durgeshriyaconstruction-sketch/astro-smart-attendance/renders/exploded_iso.png

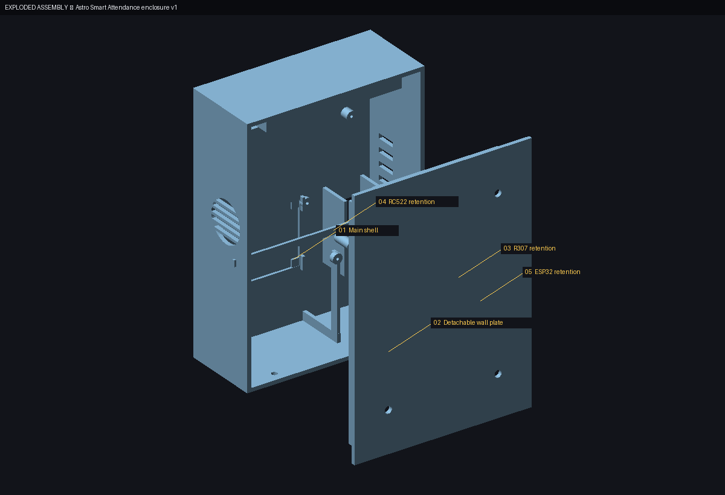
renders/exploded_iso.png
