durgeshriyaconstruction-sketch/astro-smart-attendance/renders/rfid_before_after.png

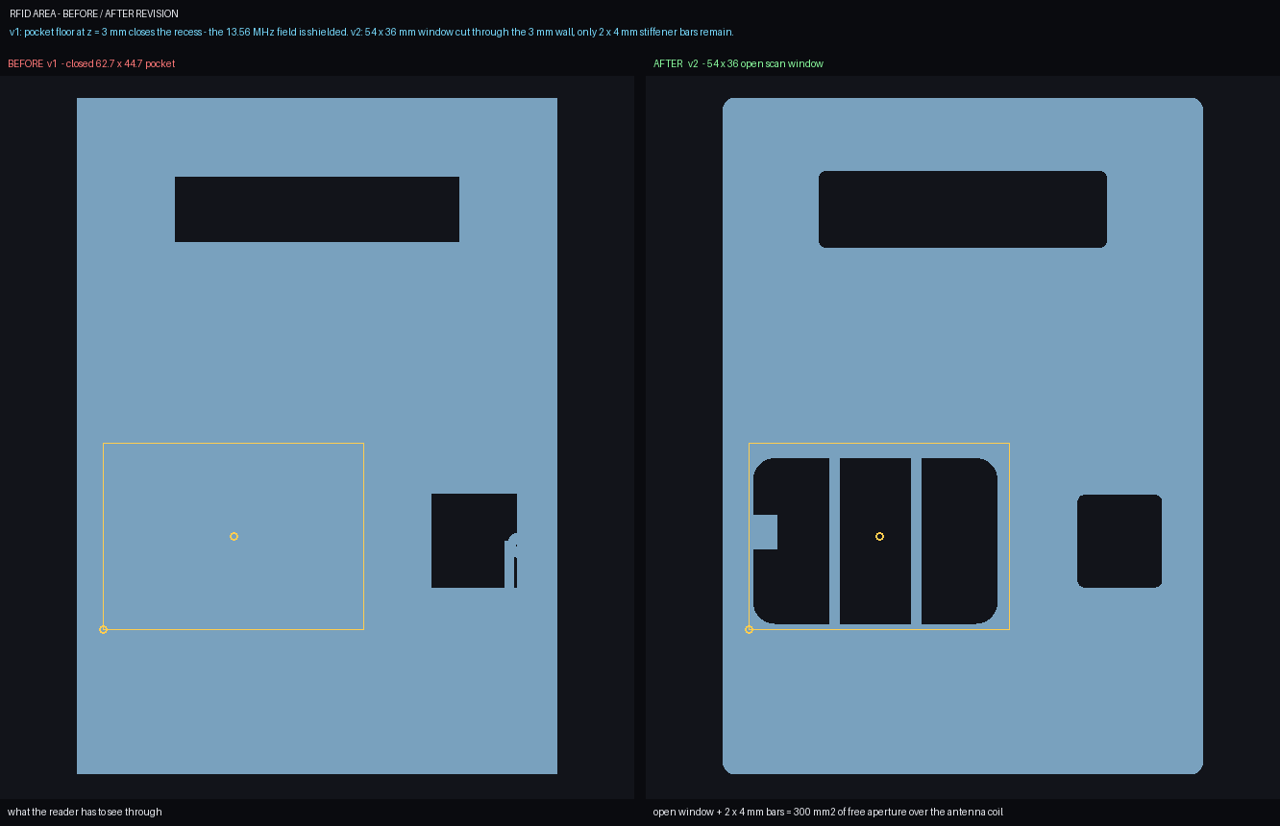
renders/rfid_before_after.png
