durgeshriyaconstruction-sketch/astro-smart-attendance/renders/section_iso.png

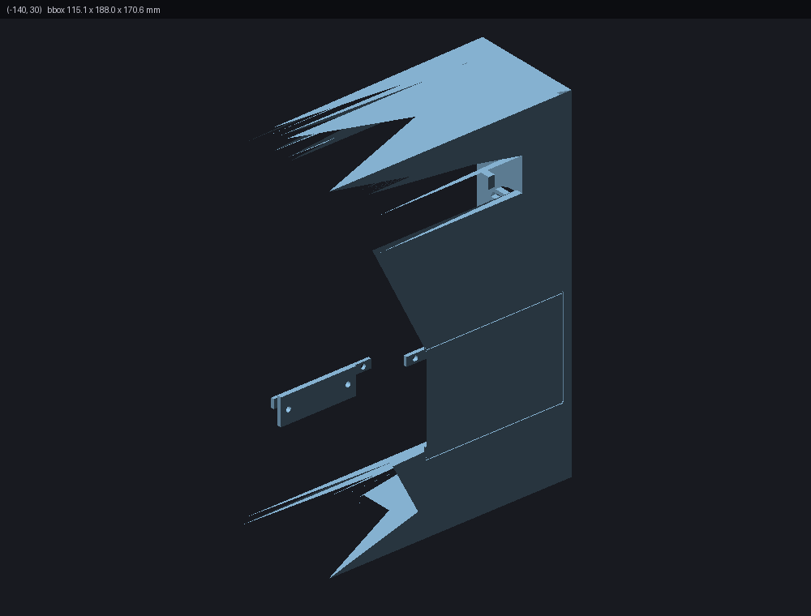
renders/section_iso.png
