durgeshriyaconstruction-sketch/astro-smart-attendance/renders/shell_drawing_sheet.png

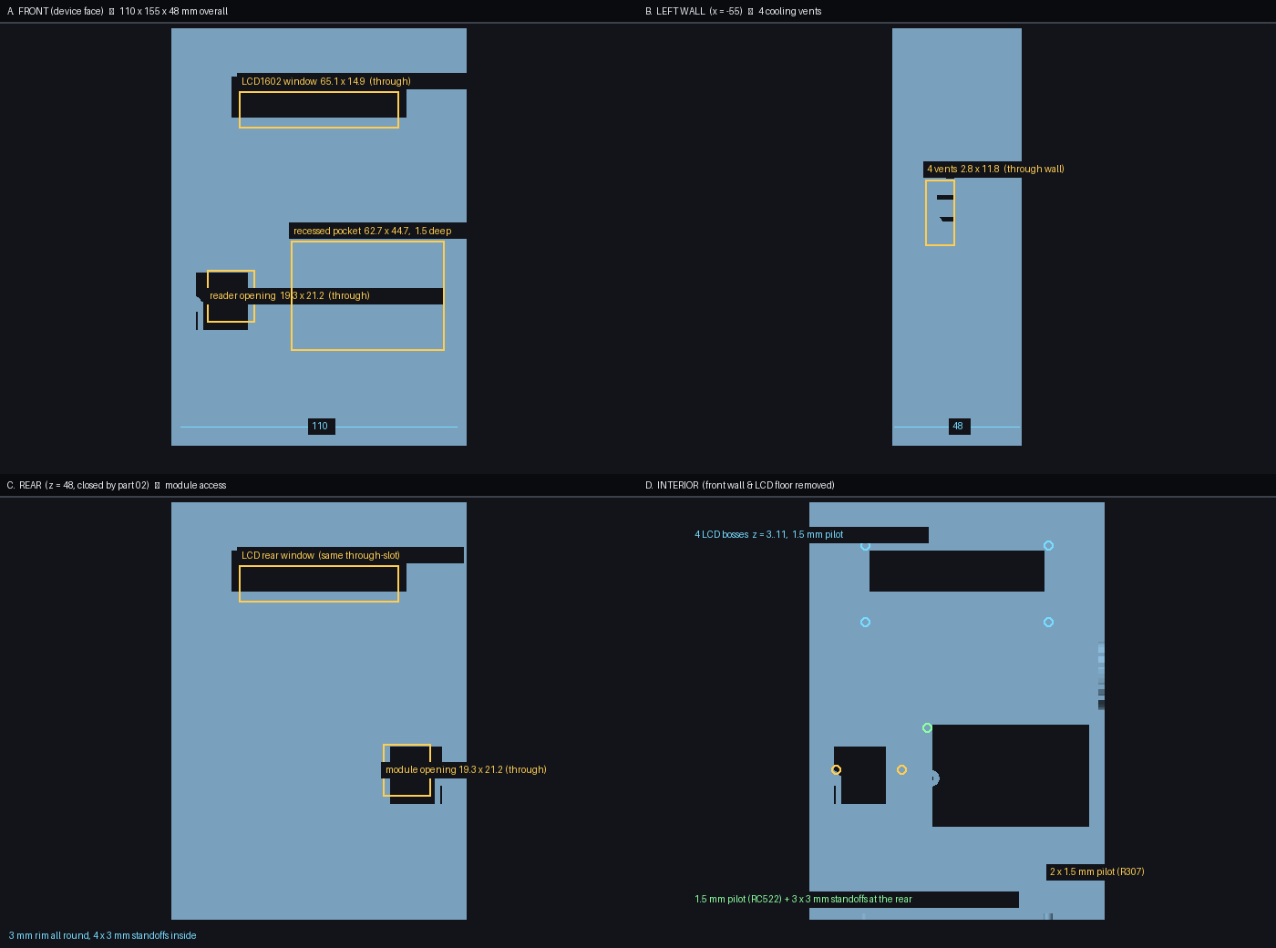
renders/shell_drawing_sheet.png
