durgeshriyaconstruction-sketch/astro-smart-attendance/renders/shell_front.png

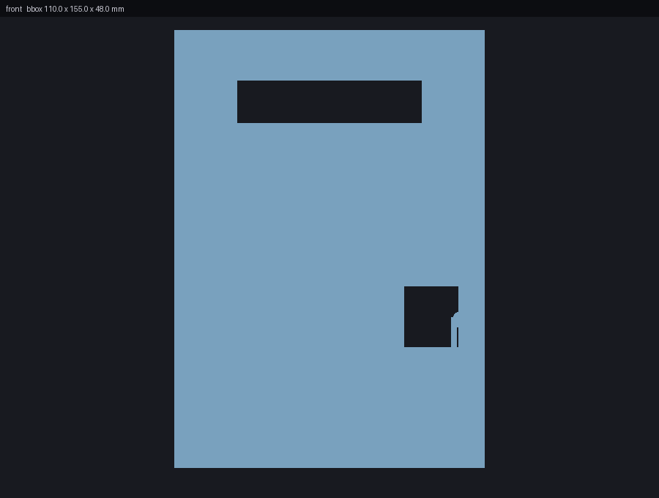
renders/shell_front.png
