durgeshriyaconstruction-sketch/astro-smart-attendance/renders/shell_iso.png

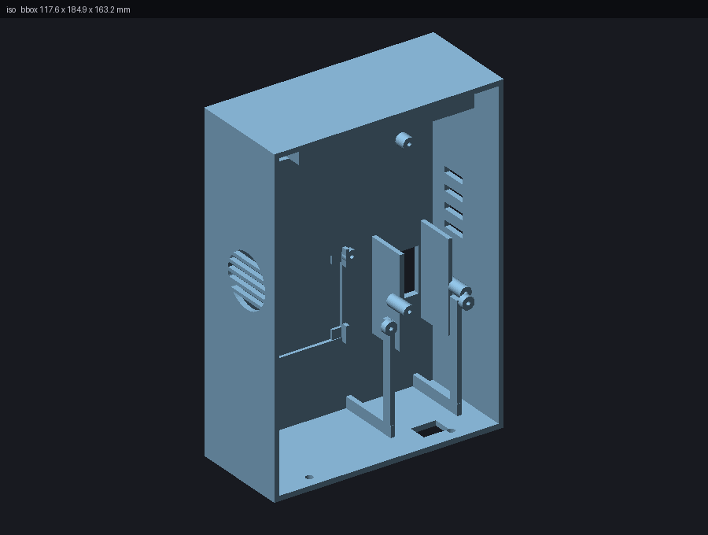
renders/shell_iso.png
