durgeshriyaconstruction-sketch/astro-smart-attendance/renders/shell_side.png

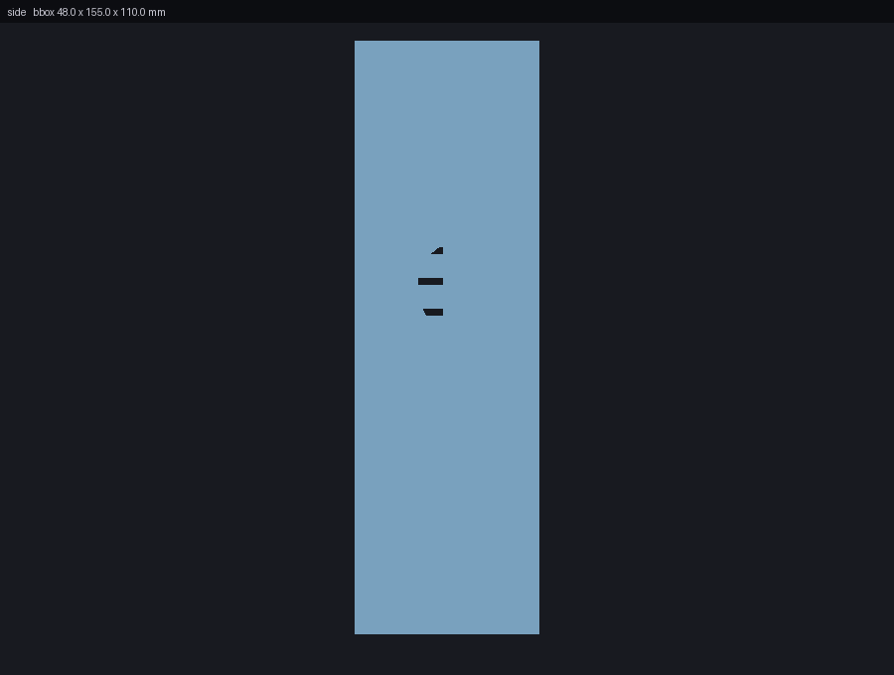
renders/shell_side.png
