durgeshriyaconstruction-sketch/astro-smart-attendance/renders/shell_top.png

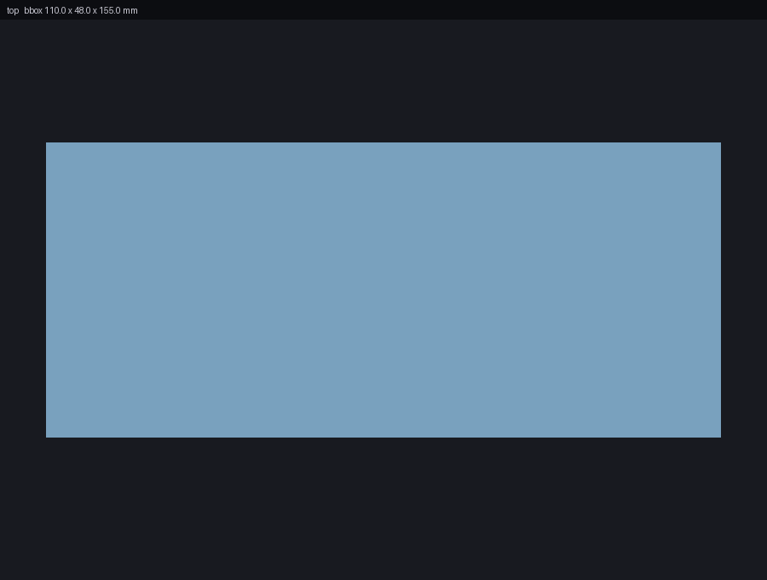
renders/shell_top.png
