durgeshriyaconstruction-sketch/astro-smart-attendance/renders/v2_all_views.png

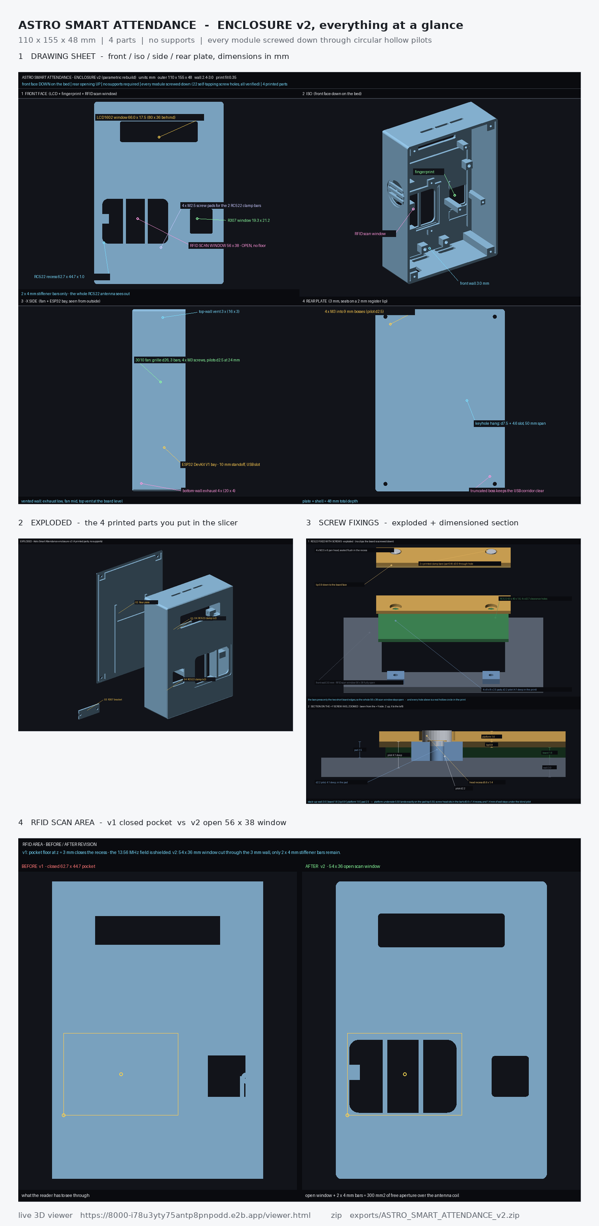
renders/v2_all_views.png
