durgeshriyaconstruction-sketch/astro-smart-attendance/renders/v2_exploded_iso.png

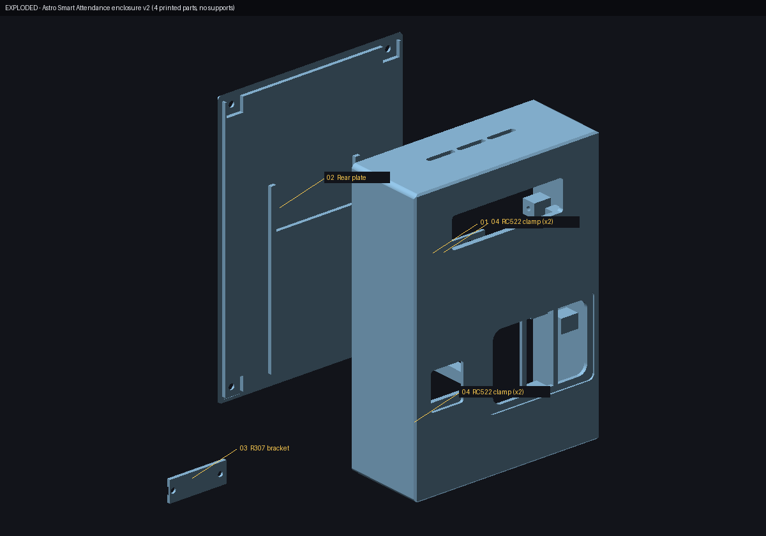
renders/v2_exploded_iso.png
