durgeshriyaconstruction-sketch/astro-smart-attendance/renders/v2_fixing_exploded.png

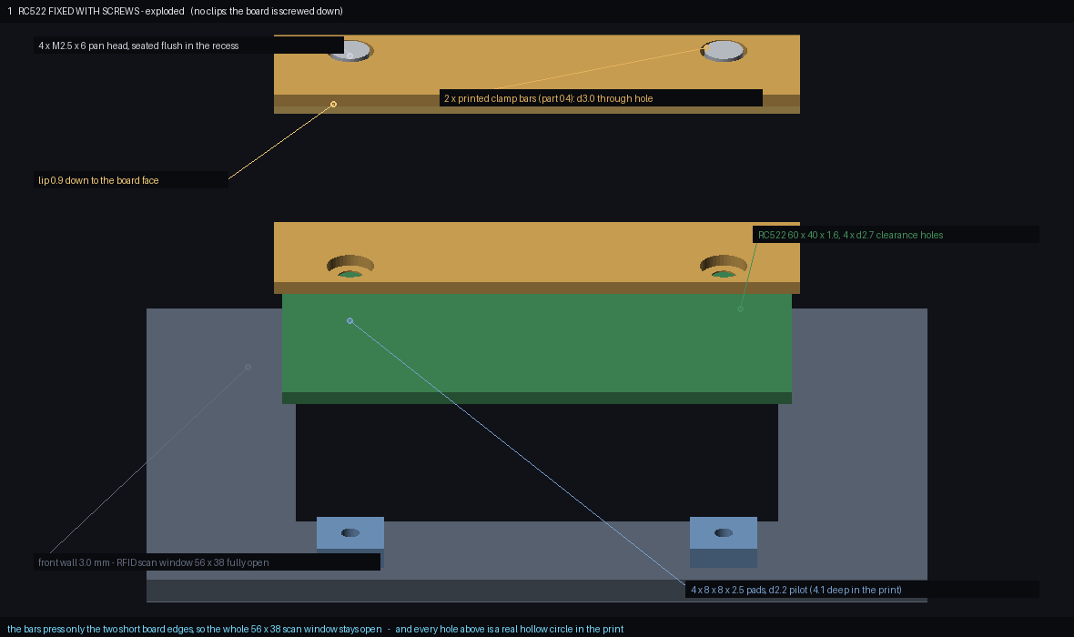
renders/v2_fixing_exploded.png
