durgeshriyaconstruction-sketch/astro-smart-attendance/renders/v2_fixing_section.png

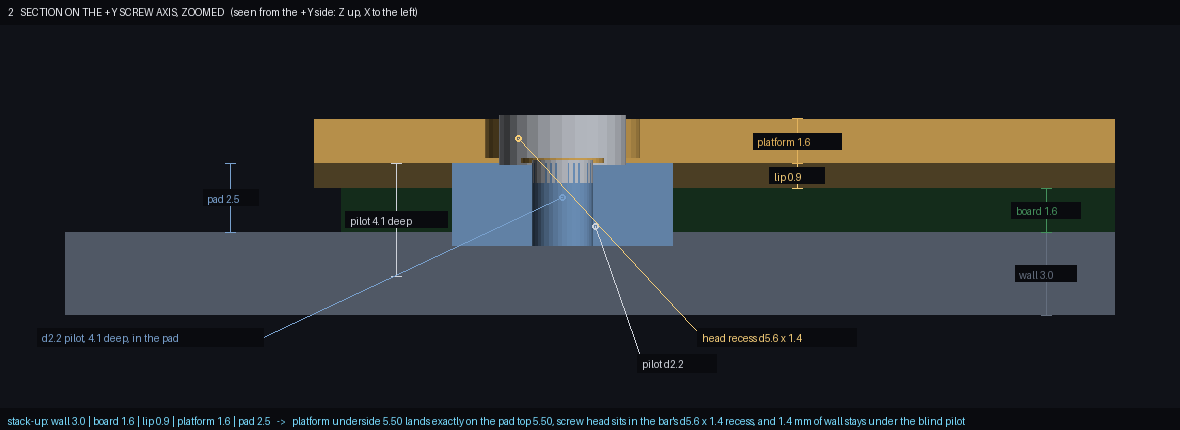
renders/v2_fixing_section.png
