durgeshriyaconstruction-sketch/astro-smart-attendance/renders/v2_shell_drawing_sheet.png

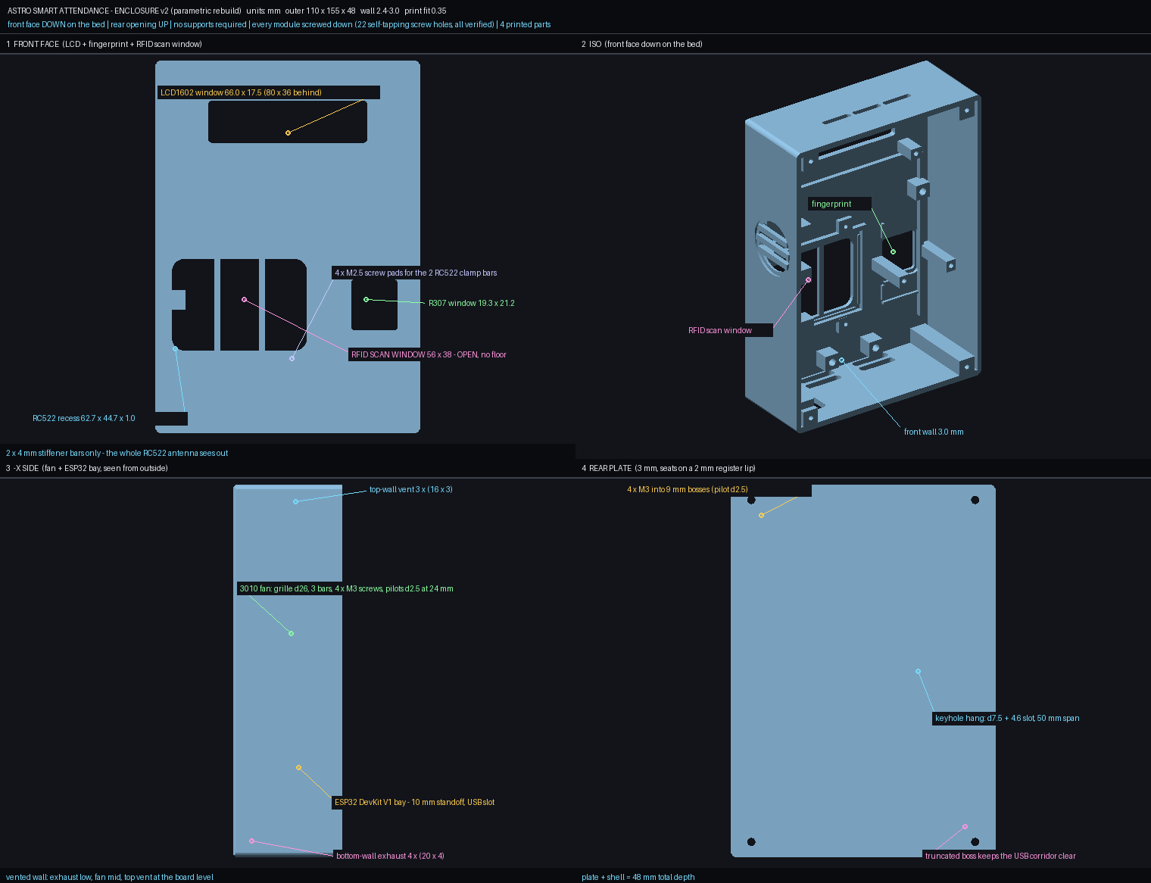
renders/v2_shell_drawing_sheet.png
