durgeshriyaconstruction-sketch/astro-smart-attendance/renders/v3_all_views.png

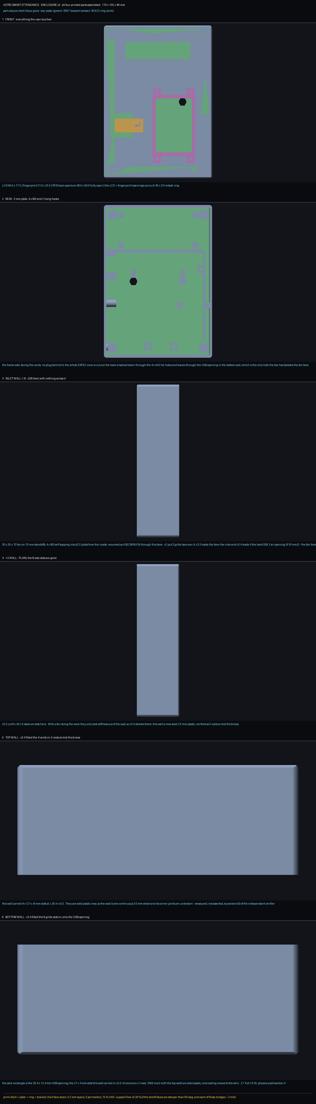
renders/v3_all_views.png
