durgeshriyaconstruction-sketch/astro-smart-attendance/renders/v3_blend_exploded.png

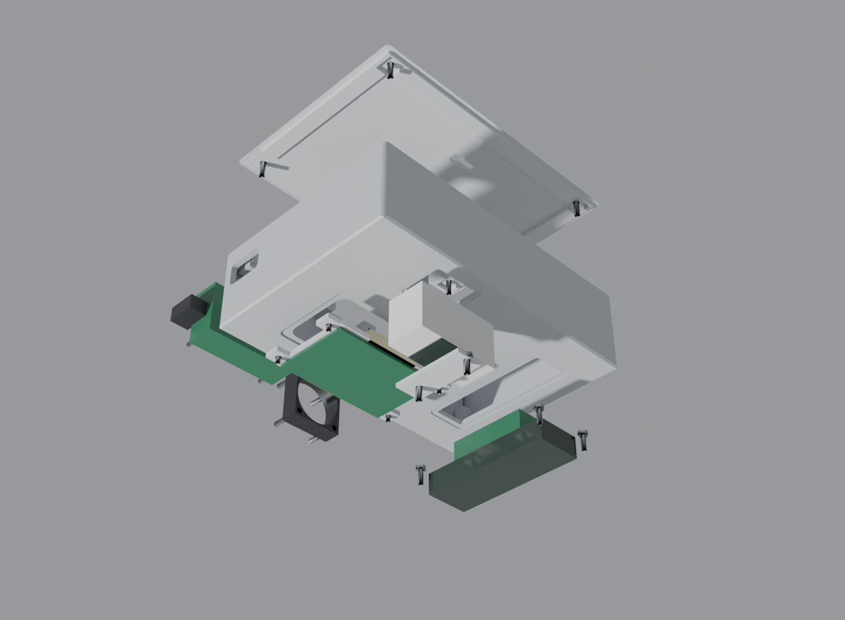
renders/v3_blend_exploded.png
