durgeshriyaconstruction-sketch/astro-smart-attendance/renders/v3_blend_front.png

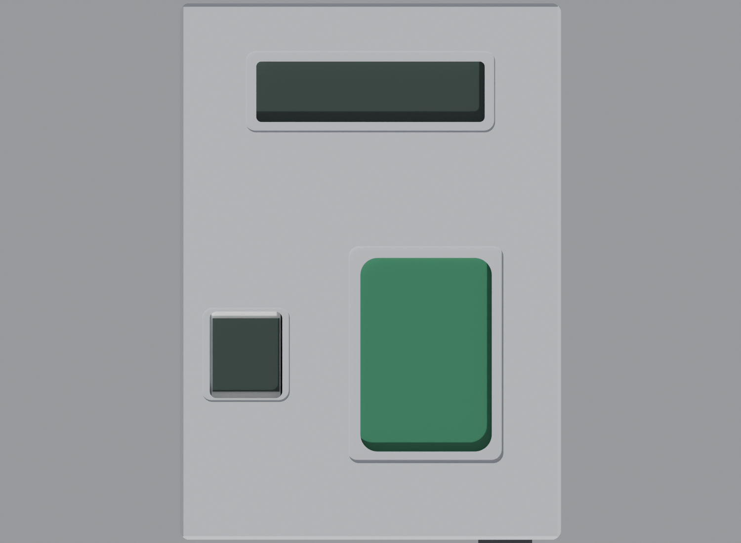
renders/v3_blend_front.png
