durgeshriyaconstruction-sketch/astro-smart-attendance/renders/v3_blend_iso.png

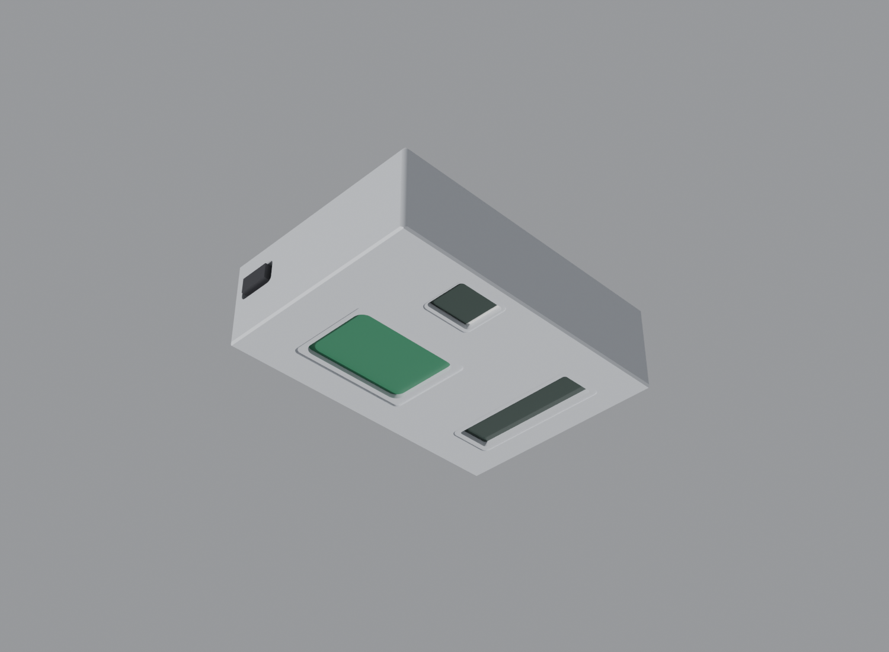
renders/v3_blend_iso.png
