durgeshriyaconstruction-sketch/astro-smart-attendance/renders/v3_fixing_detail.png

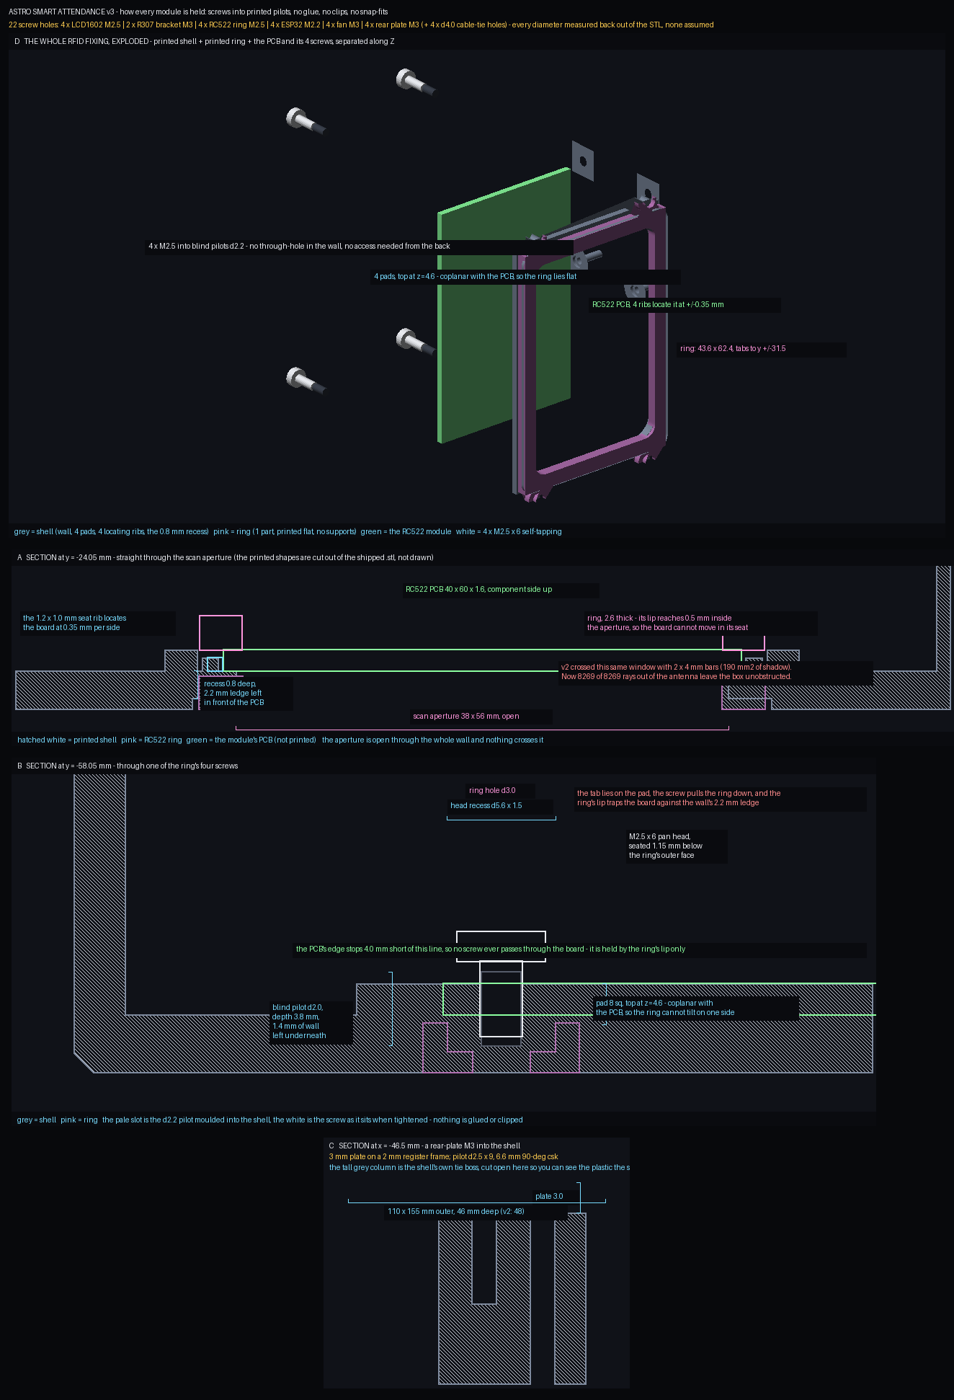
renders/v3_fixing_detail.png
