durgeshriyaconstruction-sketch/astro-smart-attendance/renders/v3_grille_map.png

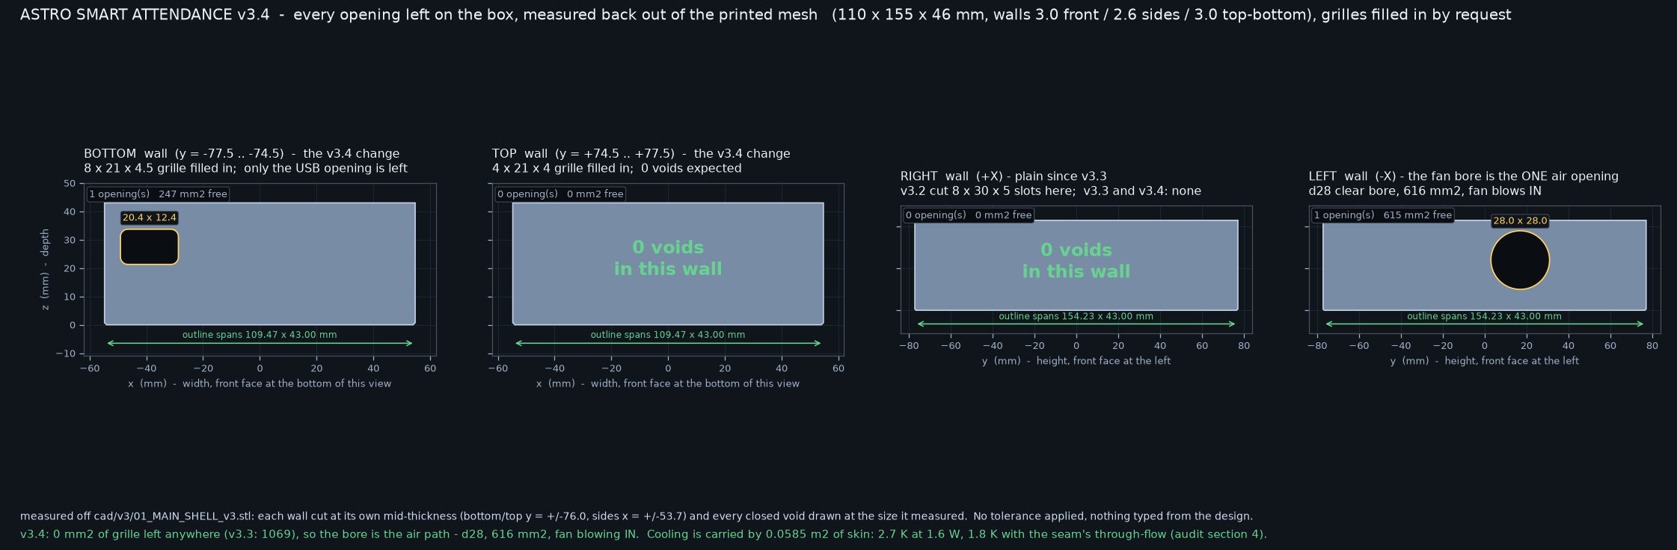
renders/v3_grille_map.png
