durgeshriyaconstruction-sketch/astro-smart-attendance/renders/v3_vs_v2.png

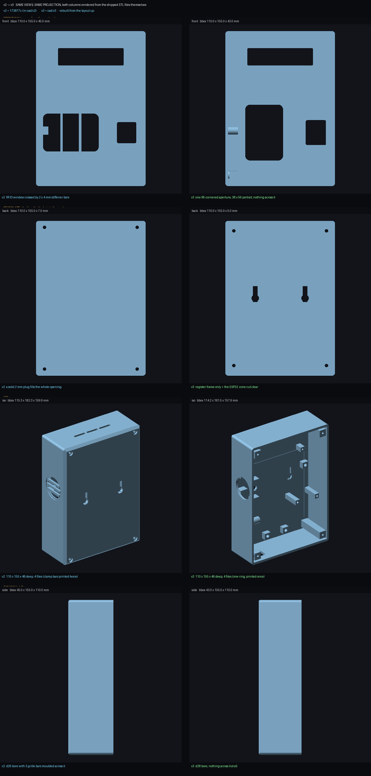
renders/v3_vs_v2.png
